jdc-cunningham/pi-zero-hq-cam/full-res-samples/16mm-blue-ring.jpg

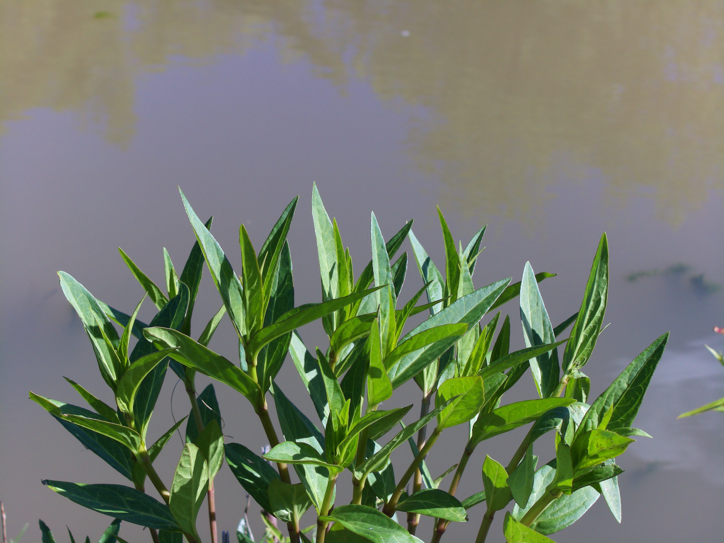
full-res-samples/16mm-blue-ring.jpg
