jdc-cunningham/pi-zero-hq-cam/full-res-samples/geese-on-lake-8-50mm-arducam.jpg

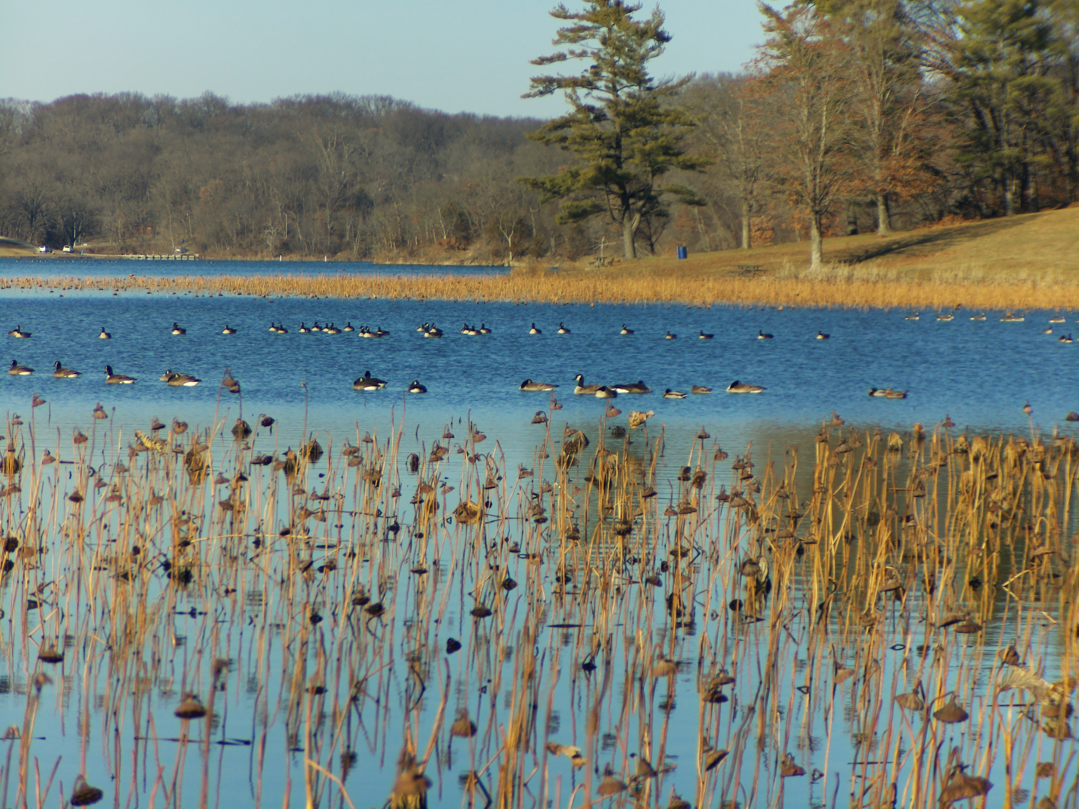
full-res-samples/geese-on-lake-8-50mm-arducam.jpg
