jdc-cunningham/pi-zero-hq-cam/full-res-samples/lake-5mm-sonew.jpg

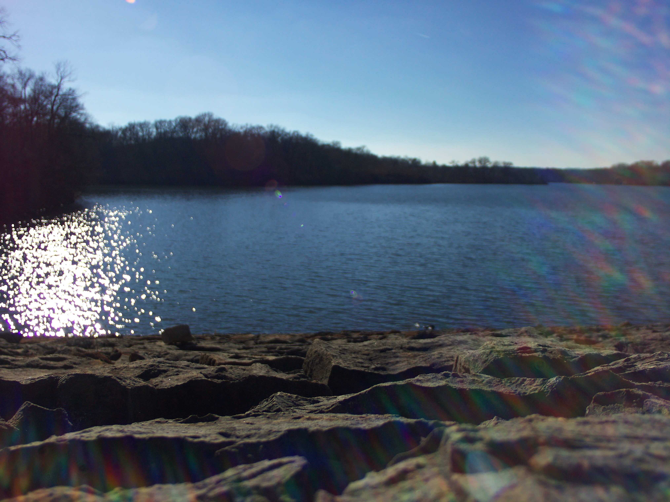
full-res-samples/lake-5mm-sonew.jpg
