jdc-cunningham/pi-zero-hq-cam/full-res-samples/macro-12mm-arducam.jpg

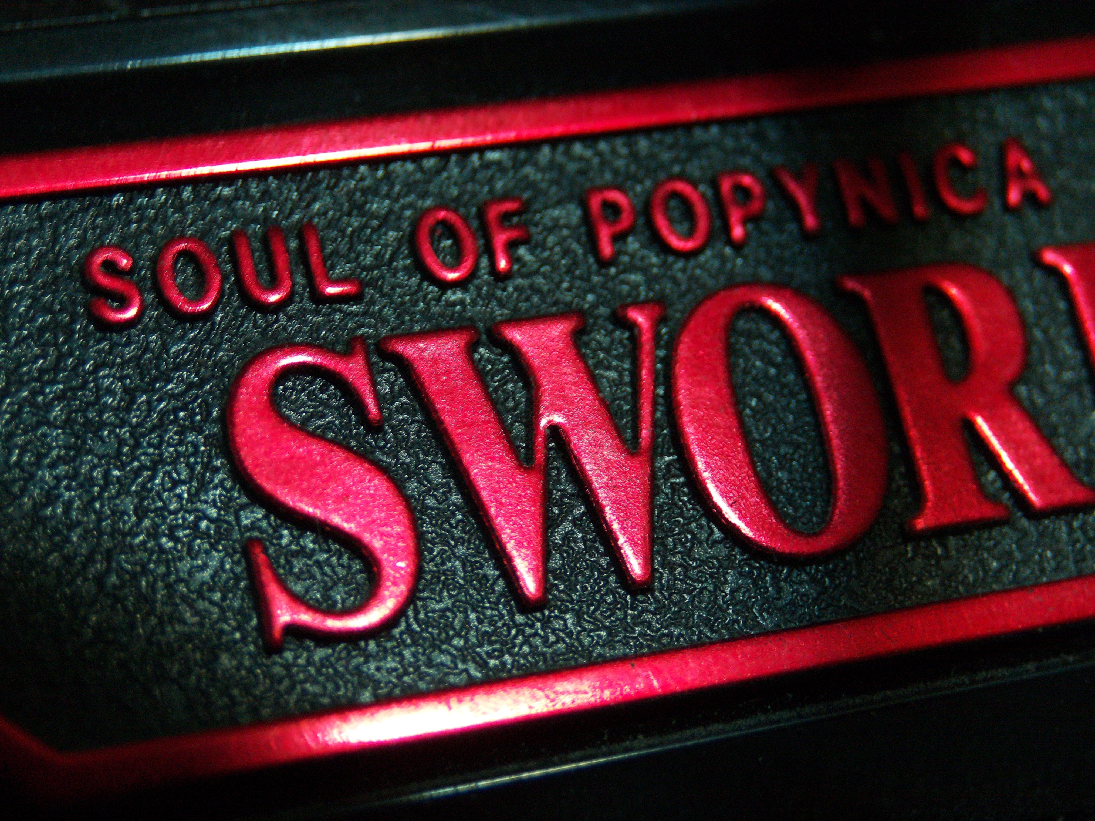
full-res-samples/macro-12mm-arducam.jpg
