jdc-cunningham/pi-zero-hq-cam/full-res-samples/tree-stump-8-50mm-arducam.jpg

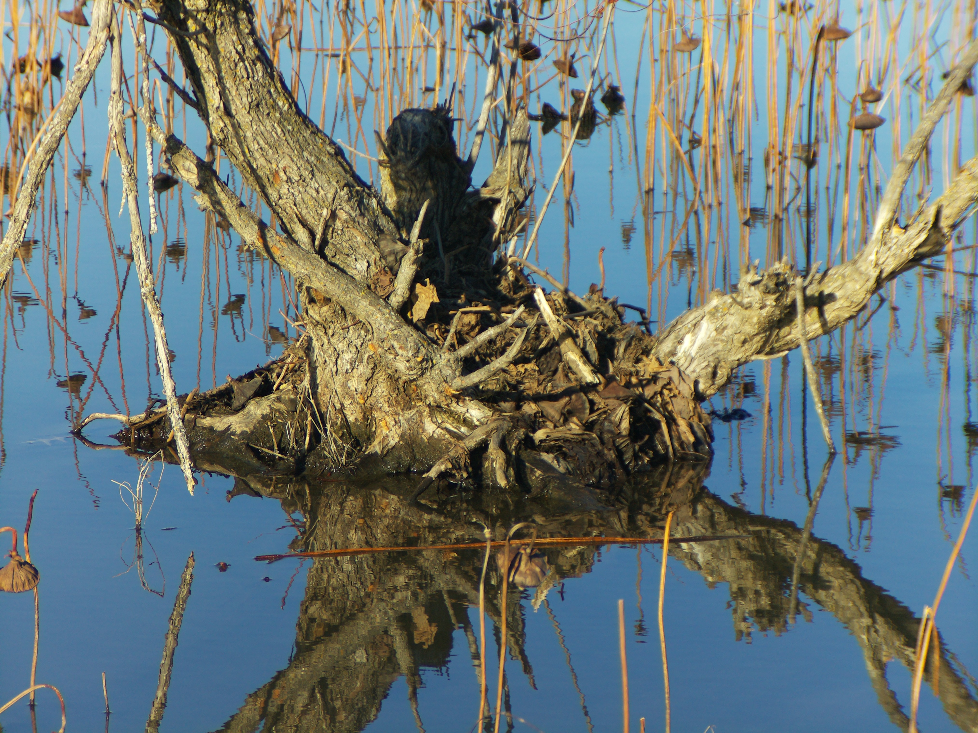
full-res-samples/tree-stump-8-50mm-arducam.jpg
