jdc-cunningham/pi-zero-hq-cam/camera/body/3d-models/stls/lens/12mm-arducam-aperture-ring.stl

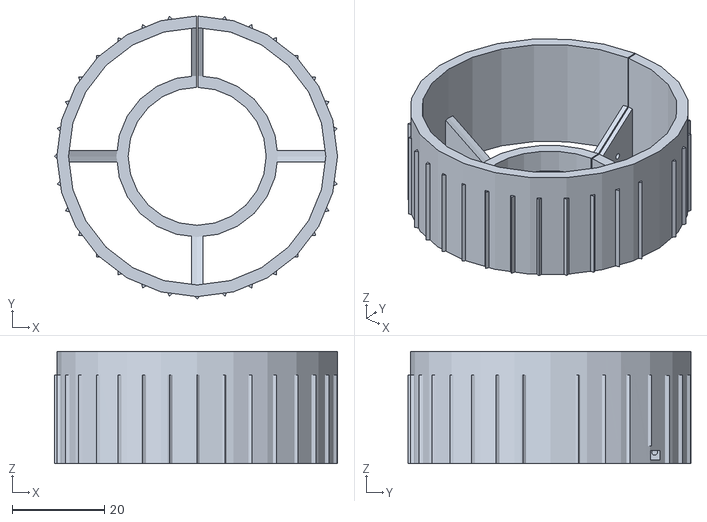
[picture p30: CAD file, 2023-12-27]
camera/body/3d-models/stls/lens/12mm-arducam-aperture-ring.stl
61.5 x 61.5 x 24.4
