jdc-cunningham/pi-zero-hq-cam/camera/body/3d-models/stls/lens/5mm-sonew-lens-cap.stl

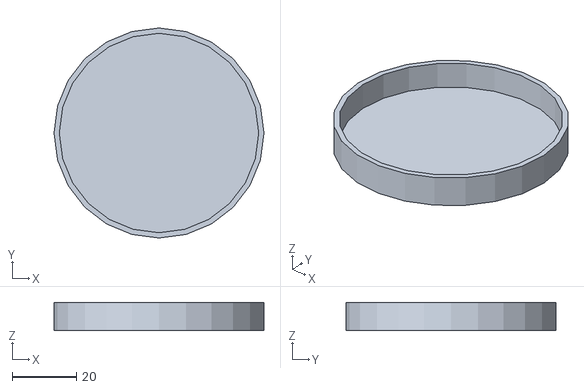
[picture p31: CAD file, 2023-12-27]
camera/body/3d-models/stls/lens/5mm-sonew-lens-cap.stl
65.5 x 65.5 x 8.89
