jdc-cunningham/pi-zero-hq-cam/camera/body/3d-models/stls/lens/8-50mm-arducam-telephoto-lens-cap.stl

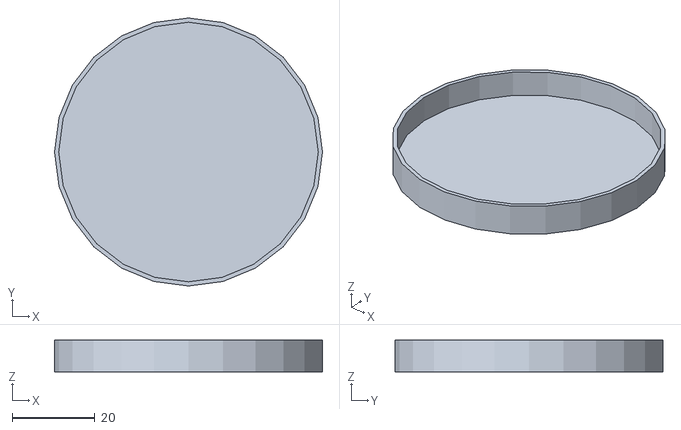
[picture p33: CAD file, 2023-12-27]
camera/body/3d-models/stls/lens/8-50mm-arducam-telephoto-lens-cap.stl
64.8 x 64.8 x 7.62
