jdc-cunningham/pi-zero-hq-cam/camera/body/3d-models/stls/lens/12mm-arducam-focus-ring.stl

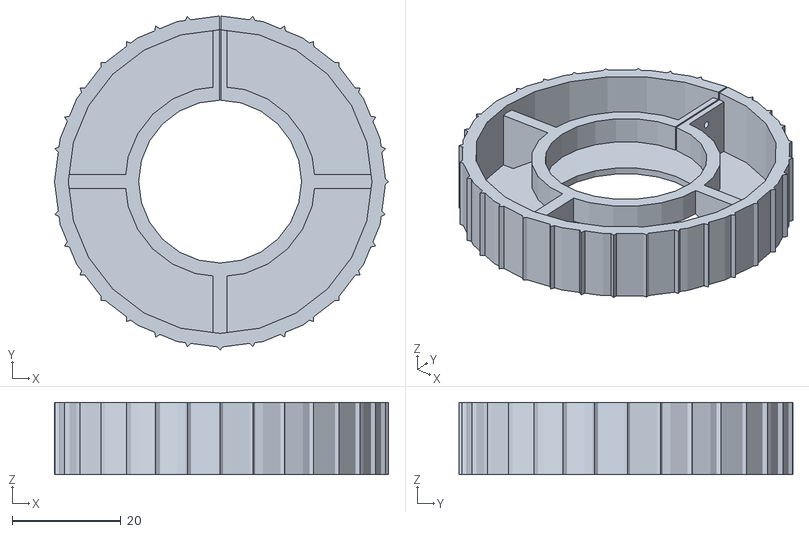
[picture p34: CAD file, 2023-12-27]
camera/body/3d-models/stls/lens/12mm-arducam-focus-ring.stl
61.5 x 61.5 x 13.3
