jdc-cunningham/pi-zero-hq-cam/camera/body/3d-models/stls/lens/8-50mm-arducam-telephoto-aperture-ring.stl

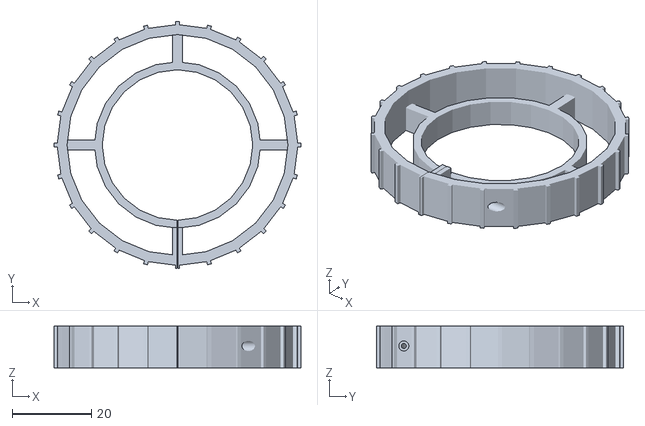
[picture p35: CAD file, 2023-12-27]
camera/body/3d-models/stls/lens/8-50mm-arducam-telephoto-aperture-ring.stl
62.5 x 62.5 x 10.5
