jdc-cunningham/pi-zero-hq-cam/camera/body/3d-models/stls/lens/5mm-barrel-ring-aperture.stl

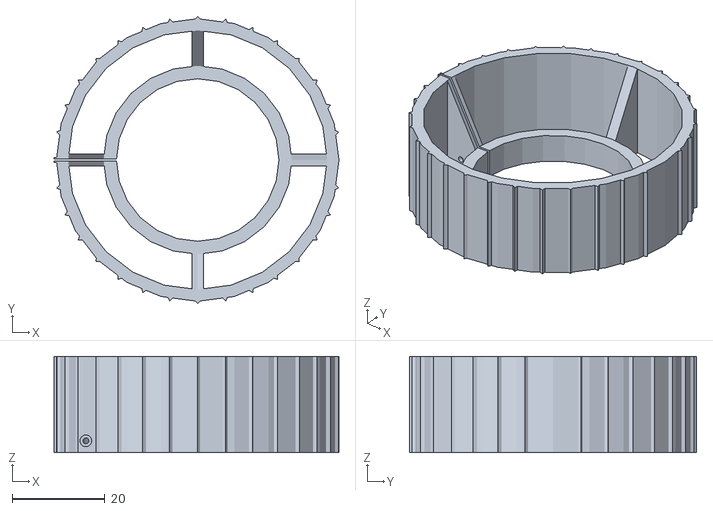
[picture p36: CAD file, 2023-12-25]
camera/body/3d-models/stls/lens/5mm-barrel-ring-aperture.stl
61.5 x 62.0 x 20.8
