jdc-cunningham/pi-zero-hq-cam/camera/body/3d-models/stls/lens/5mm-barrel-ring-focus.stl

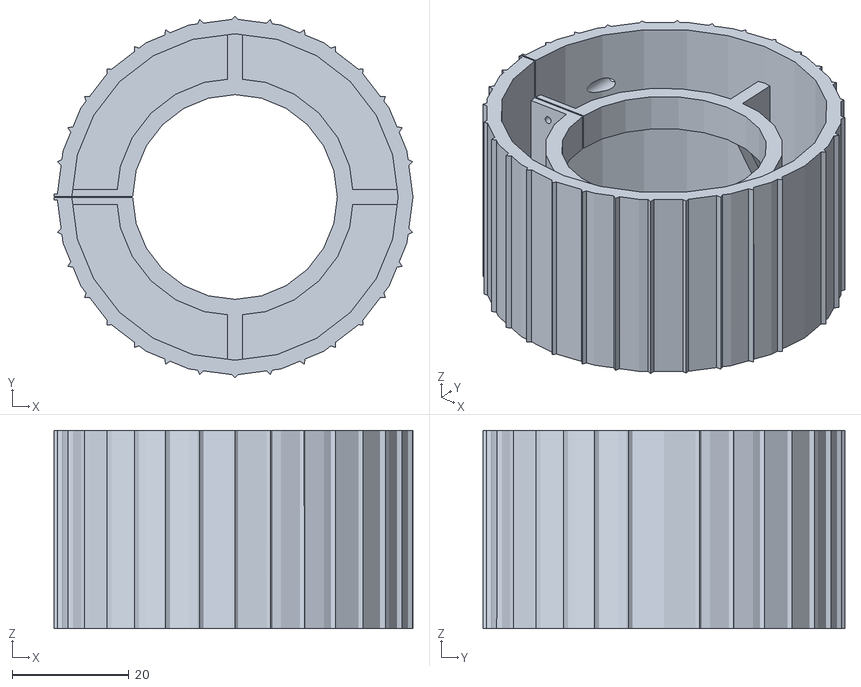
[picture p37: CAD file, 2023-12-25]
camera/body/3d-models/stls/lens/5mm-barrel-ring-focus.stl
61.5 x 62.0 x 33.9
